TannerFilip/nfc-alarm-clock/hardware/breadboard-prototype/breadboard-prototype.kicad_sch

## KiCad design hardware/breadboard-prototype/breadboard-prototype.kicad_sch (2026-09-20)

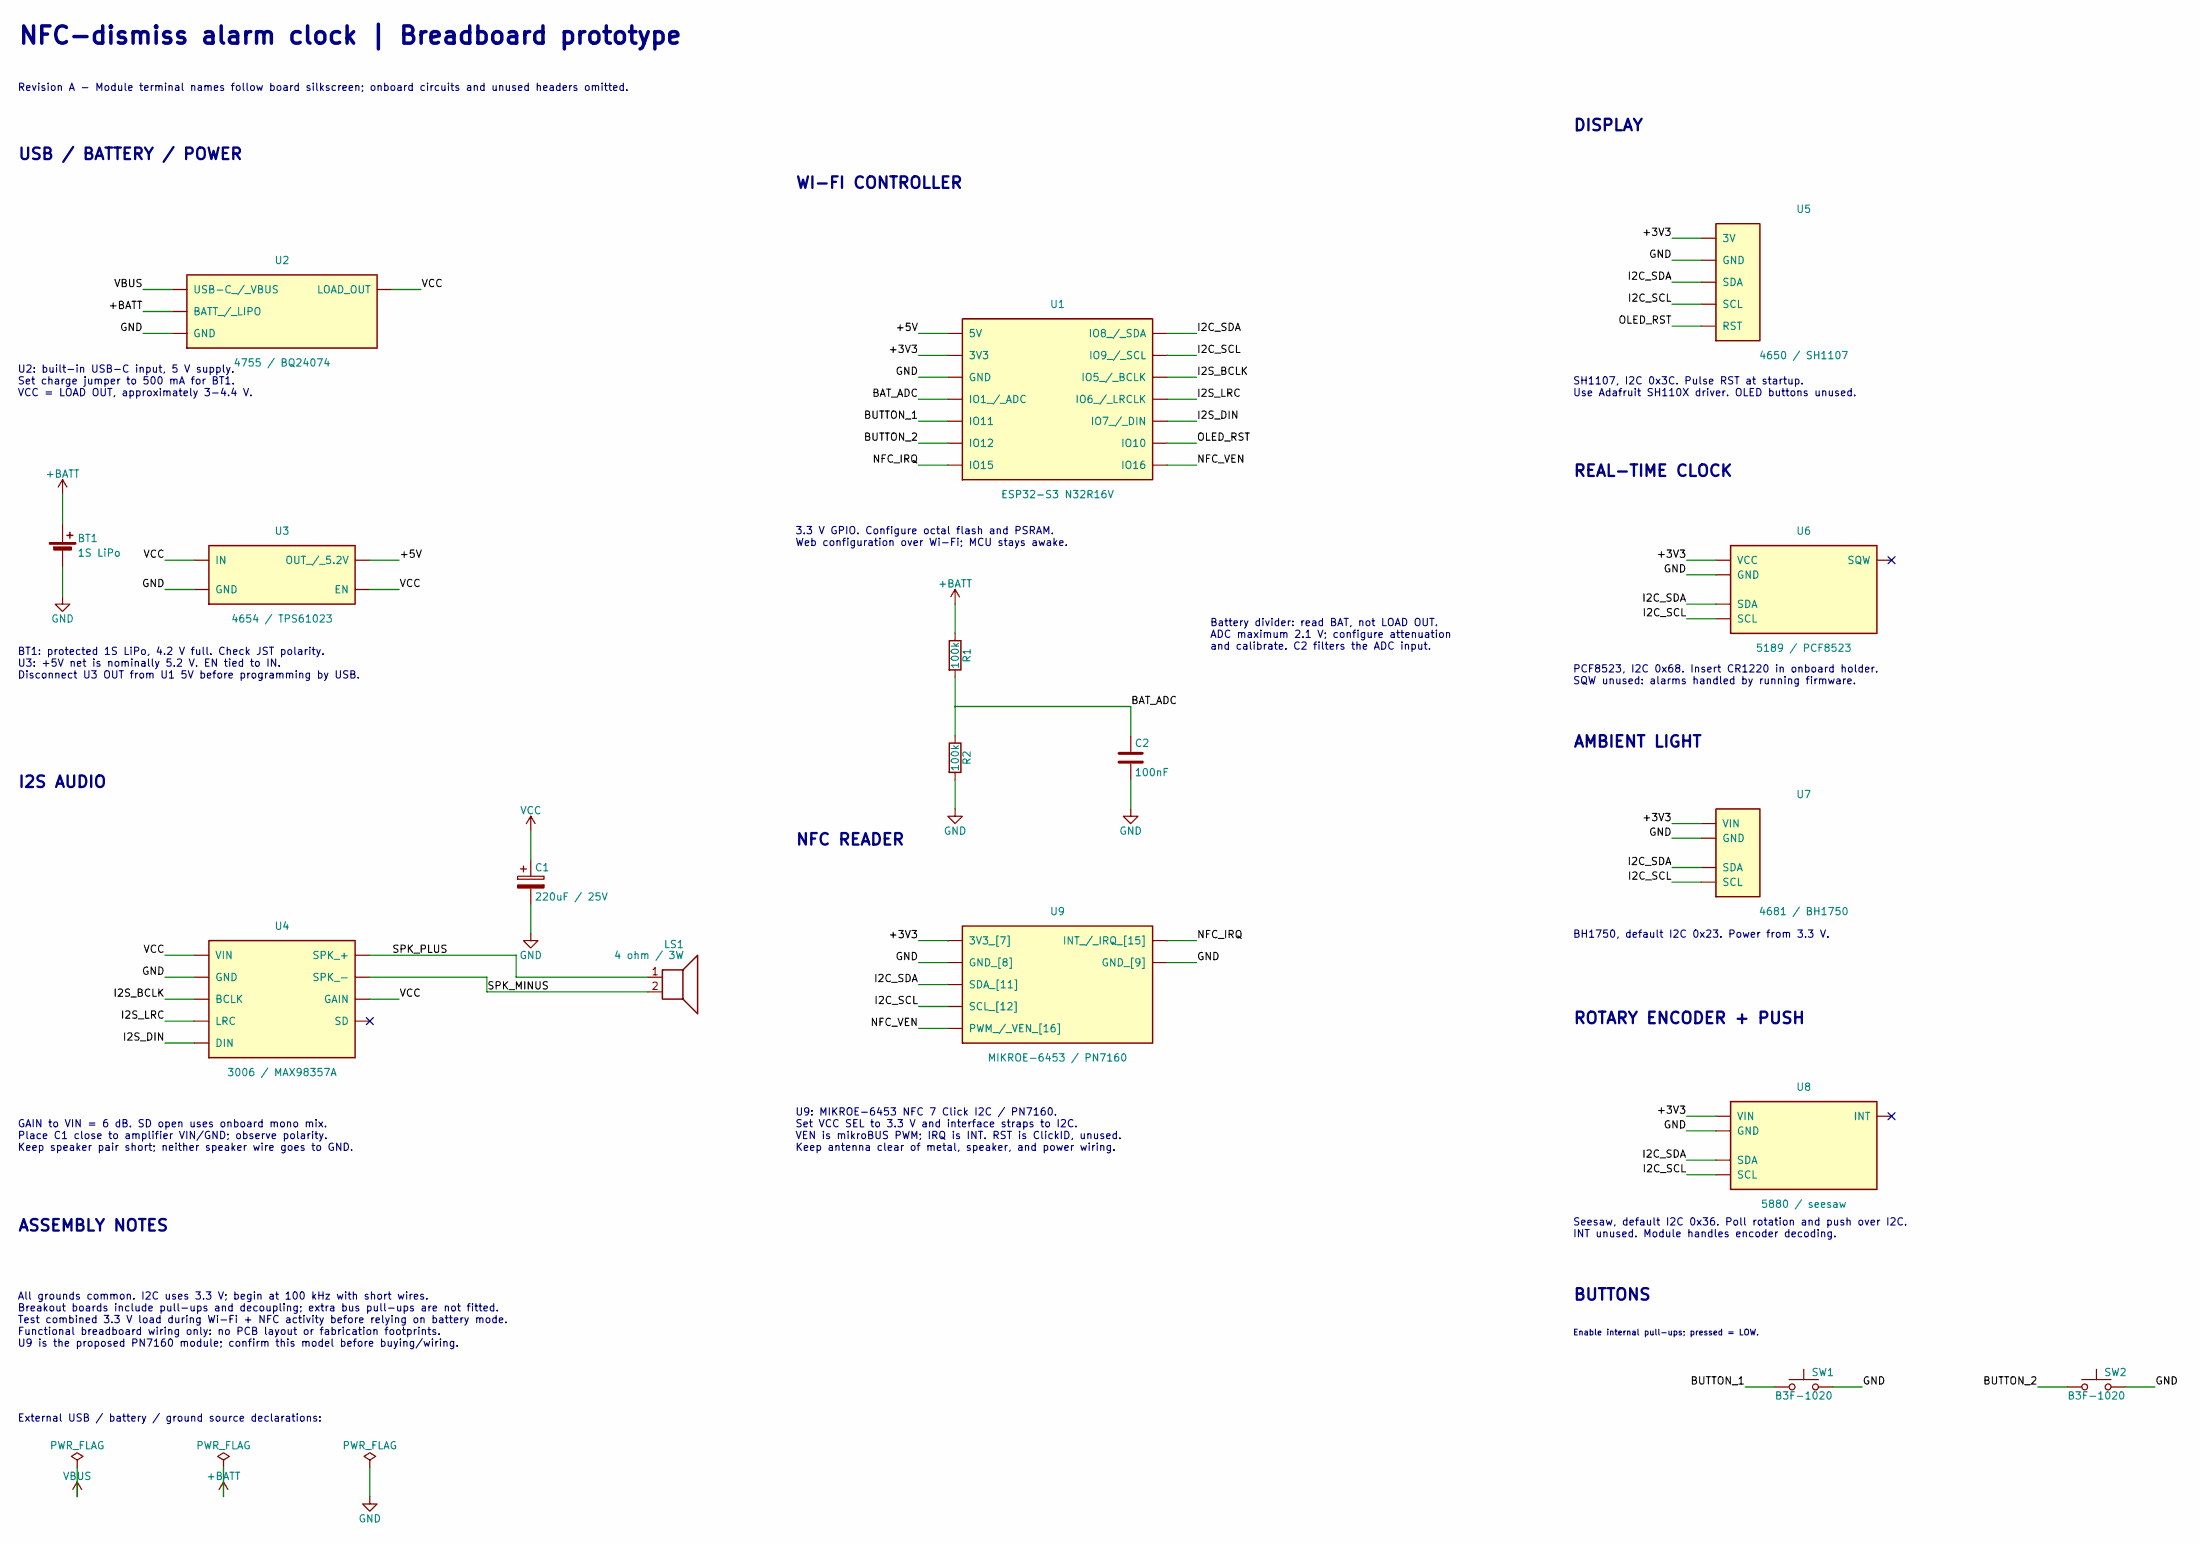
[picture p2: schematic breadboard-prototype.kicad_sch]

Parts:
BT1: 1S LiPo
C1: 220uF / 25V
C2: 100nF
LS1: 4 ohm / 3W
R1, R2: 100k
SW1, SW2: B3F-1020
U1: ESP32-S3 N32R16V
U2: 4755 / BQ24074
U3: 4654 / TPS61023
U4: 3006 / MAX98357A
U5: 4650 / SH1107
U6: 5189 / PCF8523
U7: 4681 / BH1750
U8: 5880 / seesaw
U9: MIKROE-6453 / PN7160

Connections:
+3V3: U1.3V3, U5.3V, U6.VCC, U7.VIN, U8.VIN, U9.7 (3V3_[7])
+5V: U1.5V, U3.OUT (OUT_/_5.2V)
+BATT: BT1.1 (+), BT1.2 (-), C1.2, C2.2, R1.1, R2.2, U2.BAT (BATT_/_LIPO)
BAT_ADC: C2.1, R1.2, R2.1, U1.1 (IO1_/_ADC)
BUTTON_1: SW1.1, U1.11 (IO11)
BUTTON_2: SW2.1, U1.12 (IO12)
GND: SW1.2, SW2.2, U1.GND, U2.GND, U3.GND, U4.GND, U5.GND, U6.GND, U7.GND, U8.GND, U9.8 (GND_[8]), U9.9 (GND_[9])
I2C_SCL: U1.9 (IO9_/_SCL), U5.SCL, U6.SCL, U7.SCL, U8.SCL, U9.12 (SCL_[12])
I2C_SDA: U1.8 (IO8_/_SDA), U5.SDA, U6.SDA, U7.SDA, U8.SDA, U9.11 (SDA_[11])
I2S_BCLK: U1.5 (IO5_/_BCLK), U4.BCLK
I2S_DIN: U1.7 (IO7_/_DIN), U4.DIN
I2S_LRC: U1.6 (IO6_/_LRCLK), U4.LRC
NFC_IRQ: U1.15 (IO15), U9.15 (INT_/_IRQ_[15])
NFC_VEN: U1.16 (IO16), U9.16 (PWM_/_VEN_[16])
OLED_RST: U1.10 (IO10), U5.RST
SPK_MINUS: LS1.2, U4.MINUS (SPK_-)
SPK_PLUS: LS1.1, U4.PLUS (SPK_+)
VBUS: U2.VBUS (USB-C_/_VBUS)
VCC: C1.1, U2.OUT (LOAD_OUT), U3.EN, U3.IN, U4.GAIN, U4.VIN

Notes on the sheet:
U9: MIKROE-6453 NFC 7 Click I2C / PN7160. Set VCC SEL to 3.3 V and interface straps to I2C. VEN is mikroBUS PWM; IRQ is INT. RST is ClickID, unused. Keep antenna clear of metal, speaker, and power wiring.
BH1750, default I2C 0x23. Power from 3.3 V.
DISPLAY
NFC-dismiss alarm clock | Breadboard prototype
Seesaw, default I2C 0x36. Poll rotation and push over I2C. INT unused. Module handles encoder decoding.
All grounds common. I2C uses 3.3 V; begin at 100 kHz with short wires. Breakout boards include pull-ups and decoupling; extra bus pull-ups are not fitted. Test combined 3.3 V load during Wi-Fi + NFC activity before relying on battery mode. Functional breadboard wiring only: no PCB layout or fabrica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
Enable internal pull-ups; pressed = LOW.
Battery divider: read BAT, not LOAD OUT. ADC maximum 2.1 V; configure attenuation and calibrate. C2 filters the ADC input.
WI-FI CONTROLLER
PCF8523, I2C 0x68. Insert CR1220 in onboard holder. SQW unused: alarms handled by running firmware.
I2S AUDIO
NFC READER
USB / BATTERY / POWER
REAL-TIME CLOCK
BUTTONS
SH1107, I2C 0x3C. Pulse RST at startup. Use Adafruit SH110X driver. OLED buttons unused.
ROTARY ENCODER + PUSH
GAIN to VIN = 6 dB. SD open uses onboard mono mix. Place C1 close to amplifier VIN/GND; observe polarity. Keep speaker pair short; neither speaker wire goes to GND.
3.3 V GPIO. Configure octal flash and PSRAM. Web configuration over Wi-Fi; MCU stays awake.
ASSEMBLY NOTES
AMBIENT LIGHT
U2: built-in USB-C input, 5 V supply. Set charge jumper to 500 mA for BT1. VCC = LOAD OUT, approximately 3-4.4 V.
BT1: protected 1S LiPo, 4.2 V full. Check JST polarity. U3: +5V net is nominally 5.2 V. EN tied to IN. Disconnect U3 OUT from U1 5V before programming by USB.
External USB / battery / ground source declarations:
Revision A - Module terminal names follow board silkscreen; onboard circuits and unused headers omitted.
