TannerFilip/nfc-alarm-clock/main/core/test_tone.hpp

#pragma once
#include <cstdint>

namespace clock_core {
constexpr int test_sample_rate = 16000;
constexpr int test_tone_frames = test_sample_rate * 2;
constexpr int alarm_ramp_frames = test_sample_rate * 30;
// Deliberately limited diagnostic levels, not a general volume control.
bool parse_test_level(const char* argument, uint8_t& level);
int16_t test_tone_sample(int frame, uint8_t level);
// Repeating alarm tone ramps monotonically from 1% to a validated 1-5% peak.
int16_t alarm_tone_sample(int64_t frame, uint8_t maximum_percent = 5);
}
